Ankou-B/Pulsation-vers-DTMF/Photos/Vieille photo convertisseur nu/IMG_0514.jpg

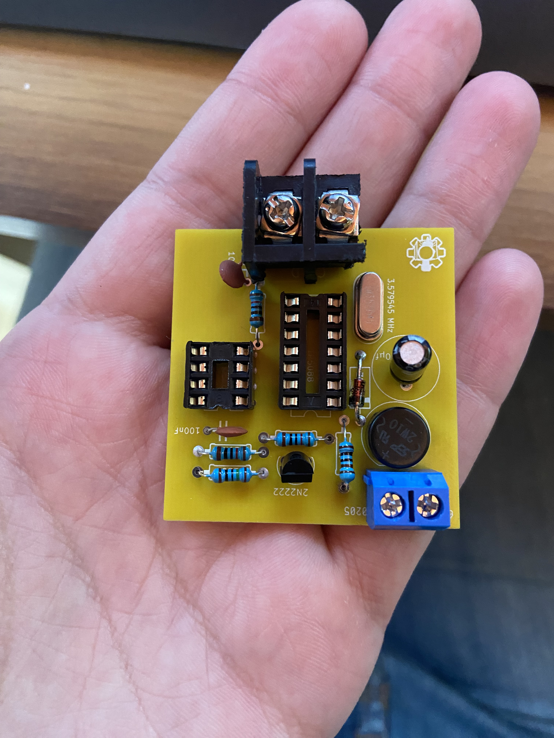
Photos/Vieille photo convertisseur nu/IMG_0514.jpg
