Ankou-B/Pulsation-vers-DTMF/Photos/Vieille photo convertisseur nu/IMG_0515.jpg

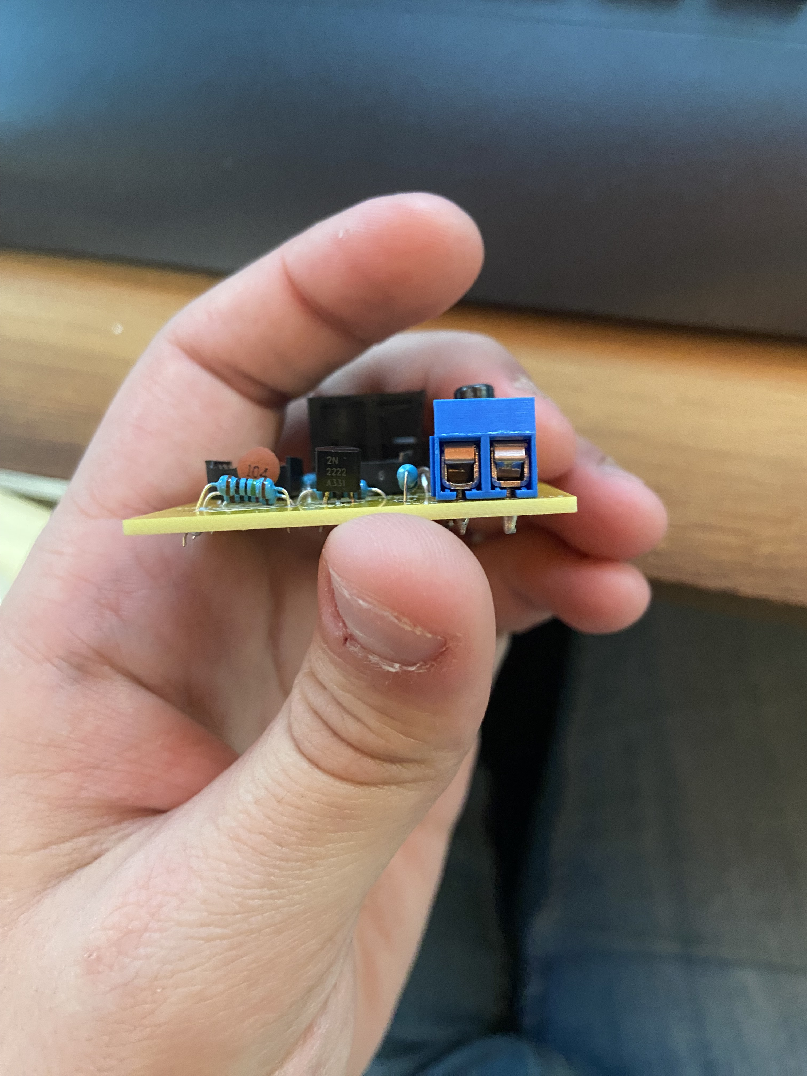
Photos/Vieille photo convertisseur nu/IMG_0515.jpg
