Ankou-B/Pulsation-vers-DTMF/Photos/Vieille photo convertisseur nu/IMG_0516.jpg

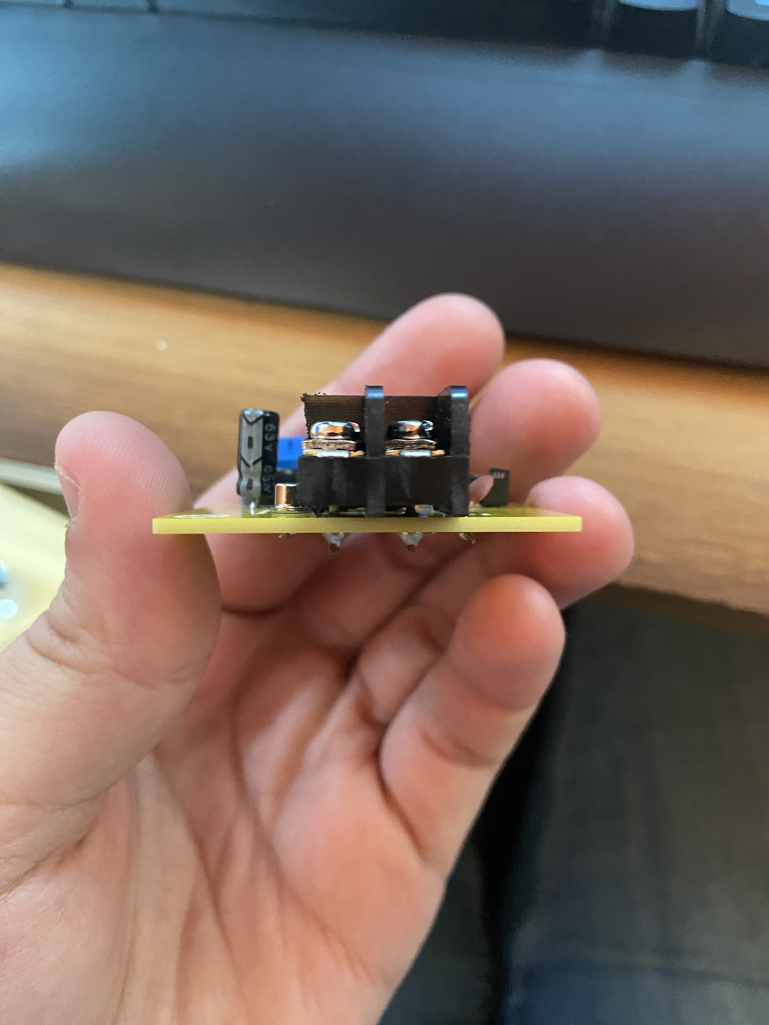
Photos/Vieille photo convertisseur nu/IMG_0516.jpg
