Ankou-B/Pulsation-vers-DTMF/Photos/Vieille photo convertisseur nu/IMG_0517.jpg

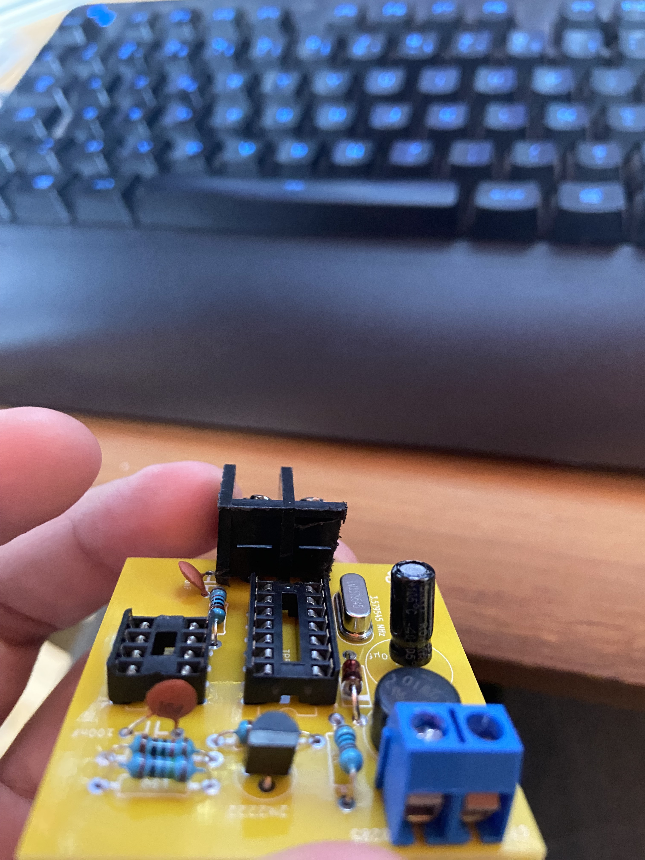
Photos/Vieille photo convertisseur nu/IMG_0517.jpg
