Ankou-B/Pulsation-vers-DTMF/Photos/Vieille photo convertisseur/1/IMG_0537.jpg

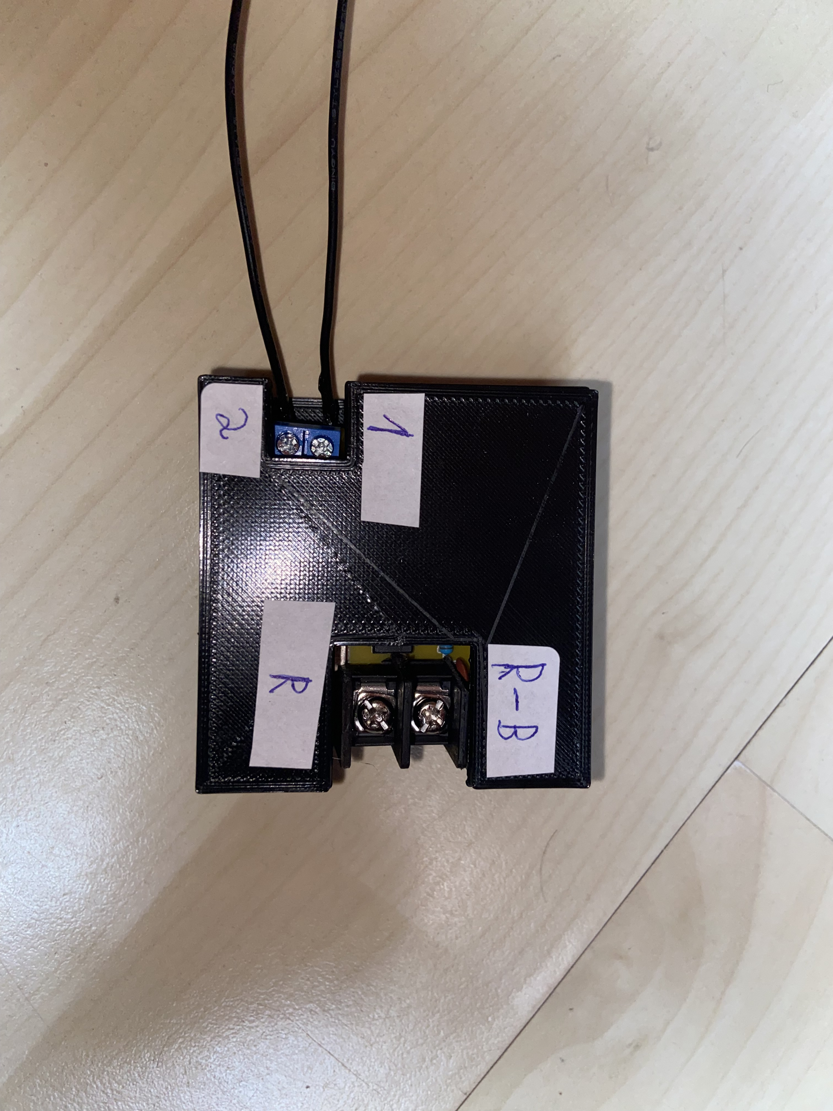
Photos/Vieille photo convertisseur/1/IMG_0537.jpg
