Ankou-B/Pulsation-vers-DTMF/Photos/Vieille photo convertisseur/2/IMG_0678.jpg

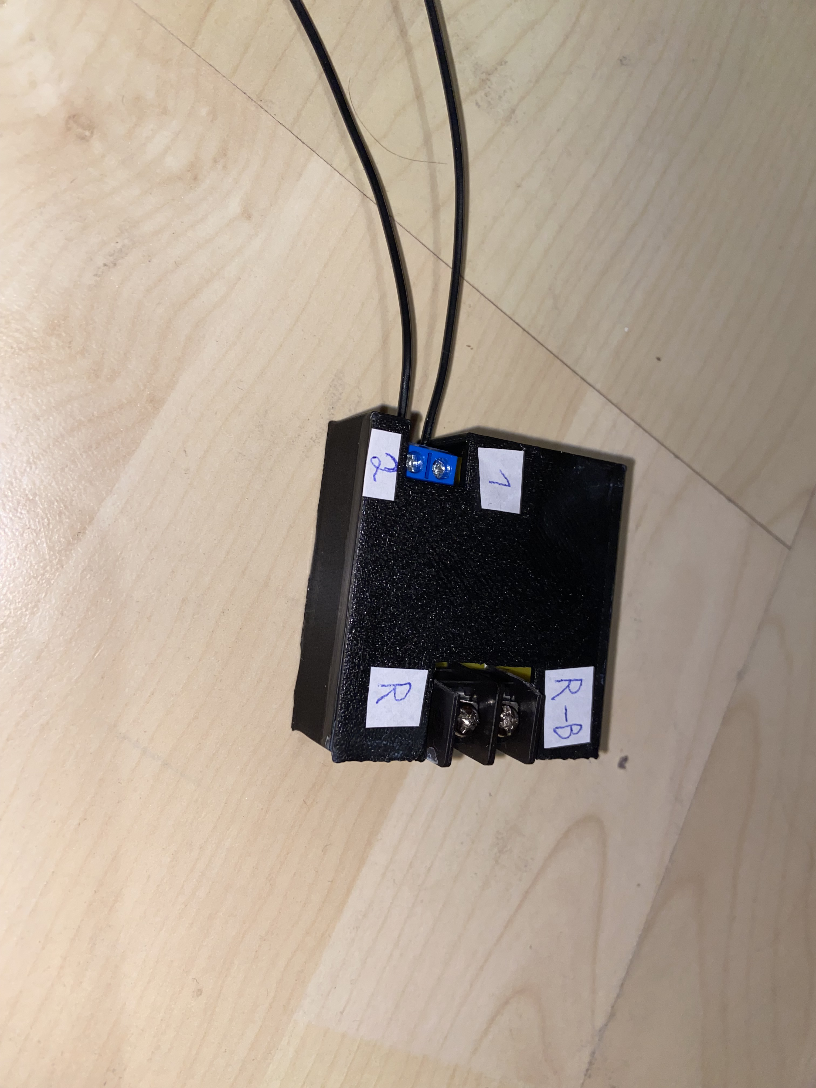
Photos/Vieille photo convertisseur/2/IMG_0678.jpg
