Ankou-B/Pulsation-vers-DTMF/Photos/Vieille photo convertisseur/3/s-l1600 (5).webp

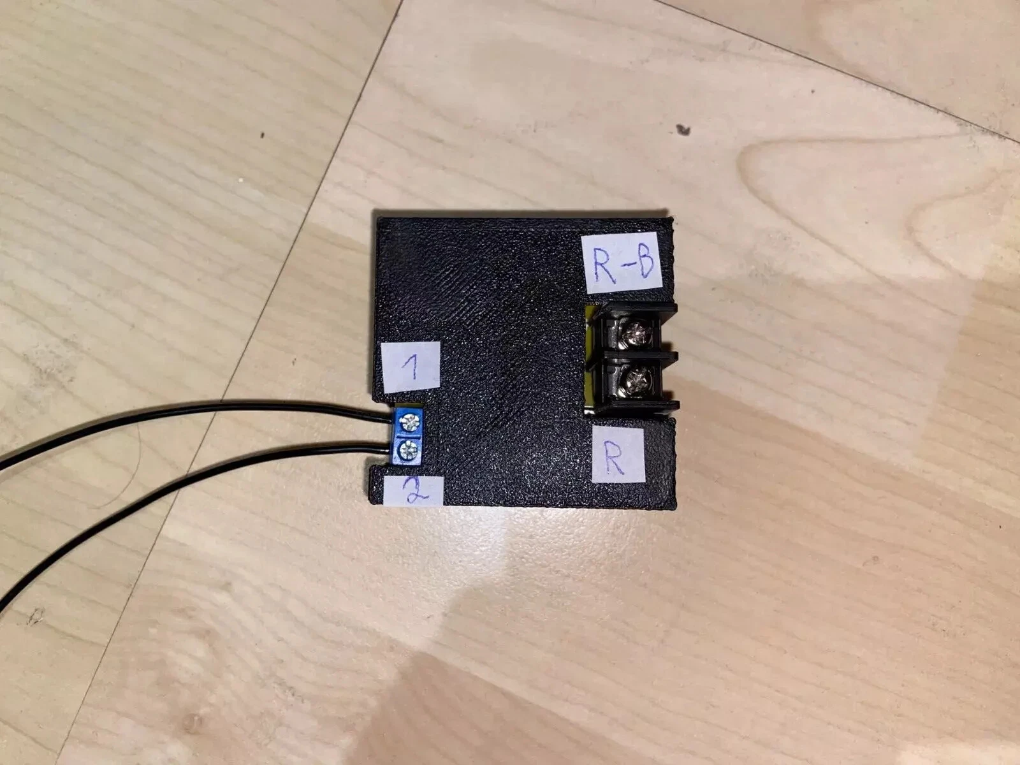
Photos/Vieille photo convertisseur/3/s-l1600 (5).webp
