Ankou-B/Pulsation-vers-DTMF/Photos/Vieille photo convertisseur/3/s-l1600 (7).webp

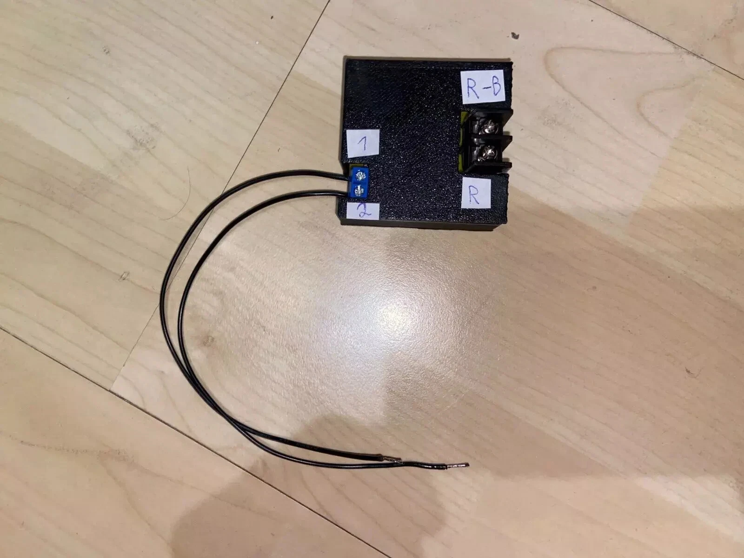
Photos/Vieille photo convertisseur/3/s-l1600 (7).webp
