Ankou-B/Pulsation-vers-DTMF/Photos/Vieille photo manuelle/IMG_0545.jpg

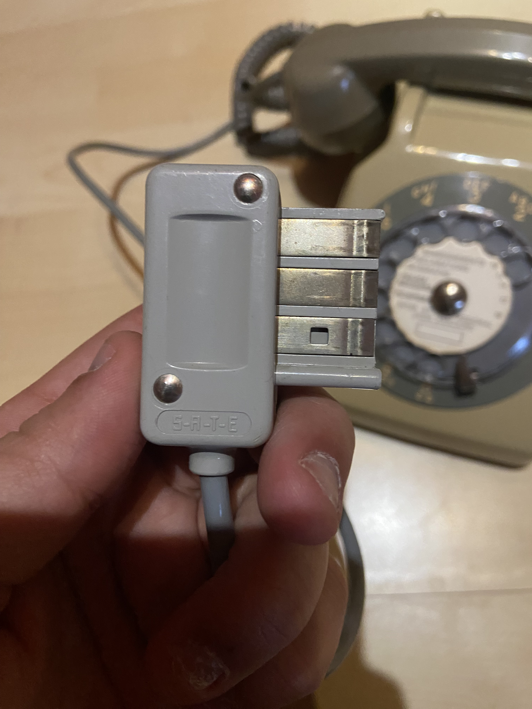
Photos/Vieille photo manuelle/IMG_0545.jpg
