Ankou-B/Pulsation-vers-DTMF/Photos/Vieille photo manuelle/IMG_0551.jpg

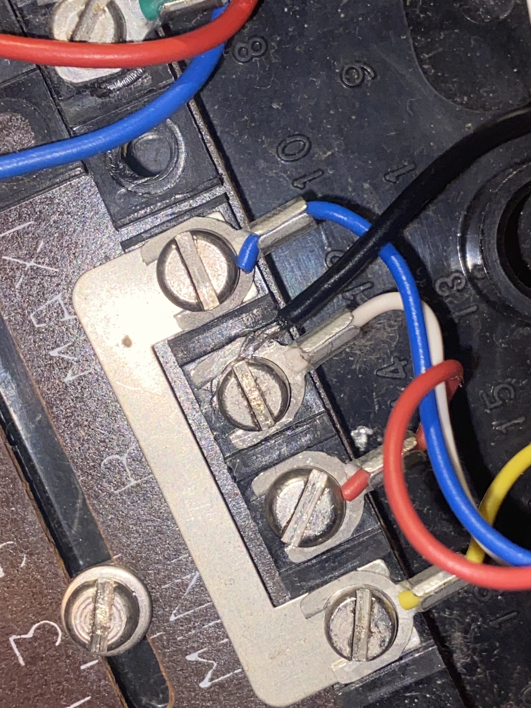
Photos/Vieille photo manuelle/IMG_0551.jpg
