Ankou-B/Pulsation-vers-DTMF/Photos/Vieille photo manuelle/IMG_0556.jpg

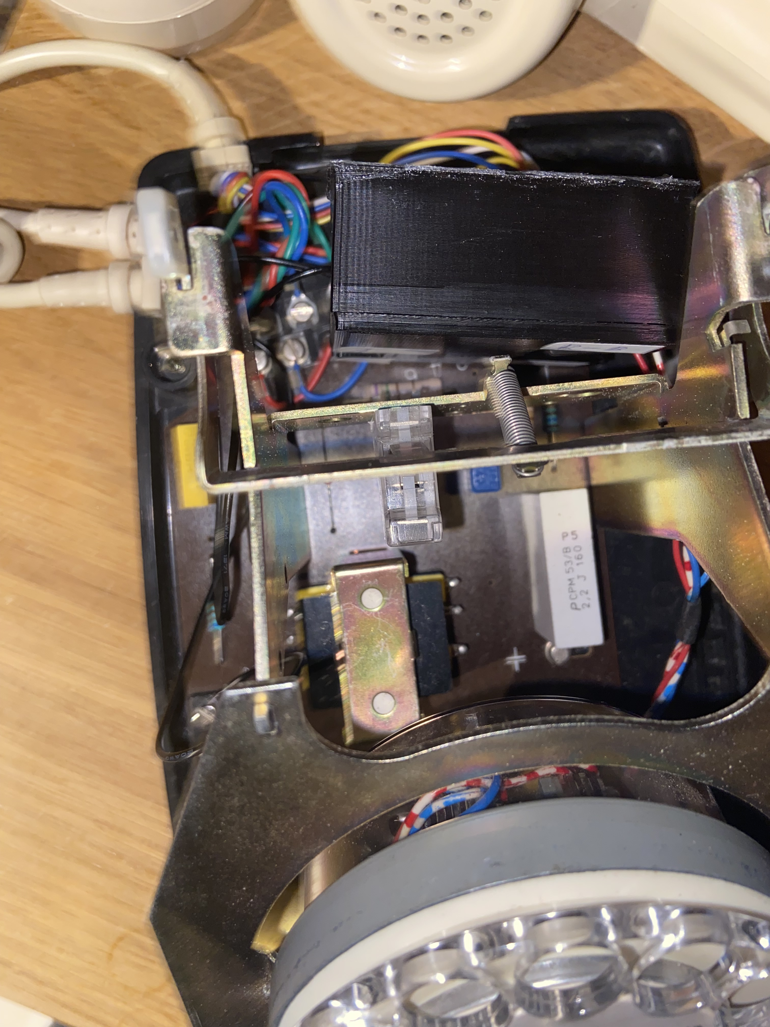
Photos/Vieille photo manuelle/IMG_0556.jpg
