Ankou-B/Pulsation-vers-DTMF/Photos/Vieille photo manuelle/IMG_0557.jpg

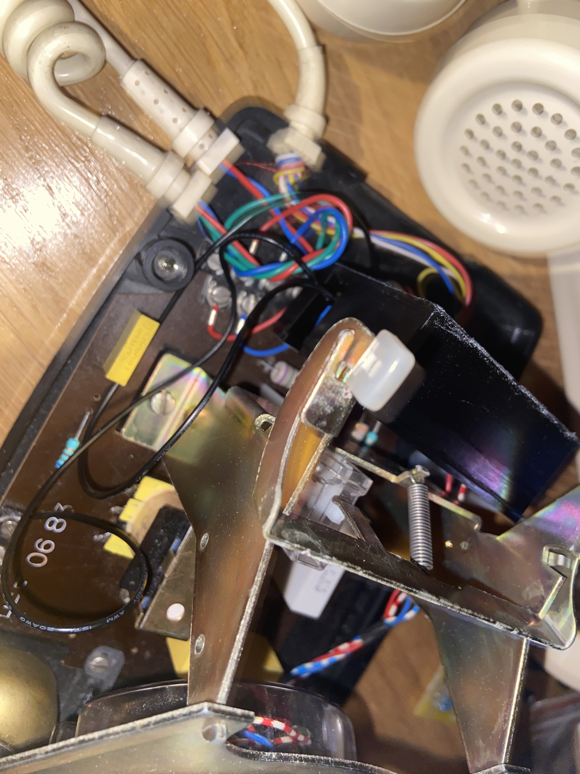
Photos/Vieille photo manuelle/IMG_0557.jpg
