Ankou-B/Pulsation-vers-DTMF/Photos/Vieille photo manuelle/IMG_0559.jpg

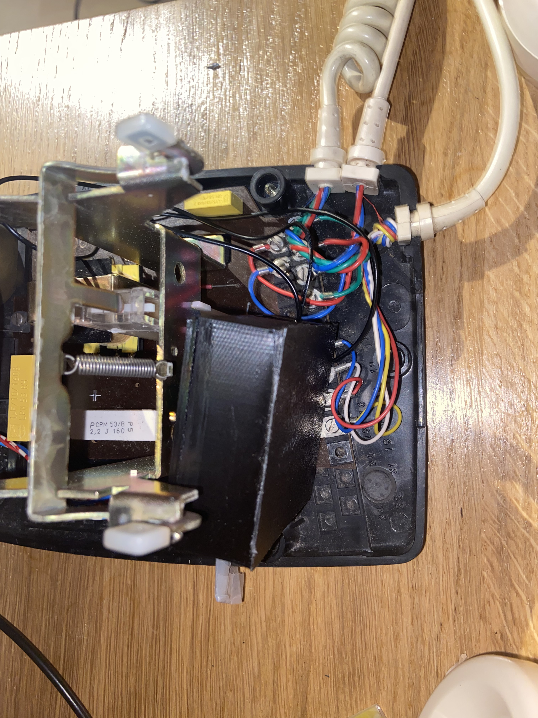
Photos/Vieille photo manuelle/IMG_0559.jpg
