Ankou-B/Pulsation-vers-DTMF/Photos/Vieille photo manuelle/IMG_0560.jpg

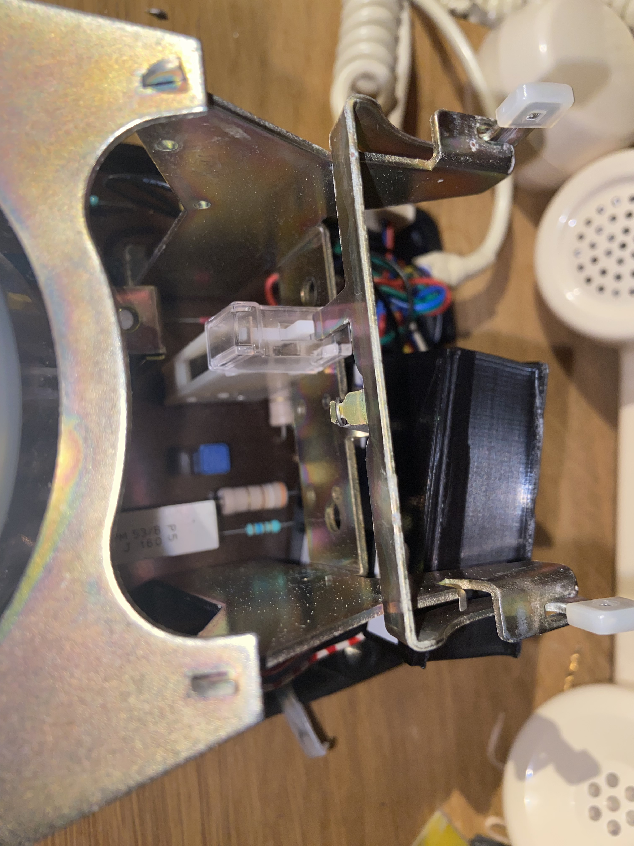
Photos/Vieille photo manuelle/IMG_0560.jpg
