Ankou-B/Pulsation-vers-DTMF/Photos/Vieille photo manuelle/IMG_0569.jpg

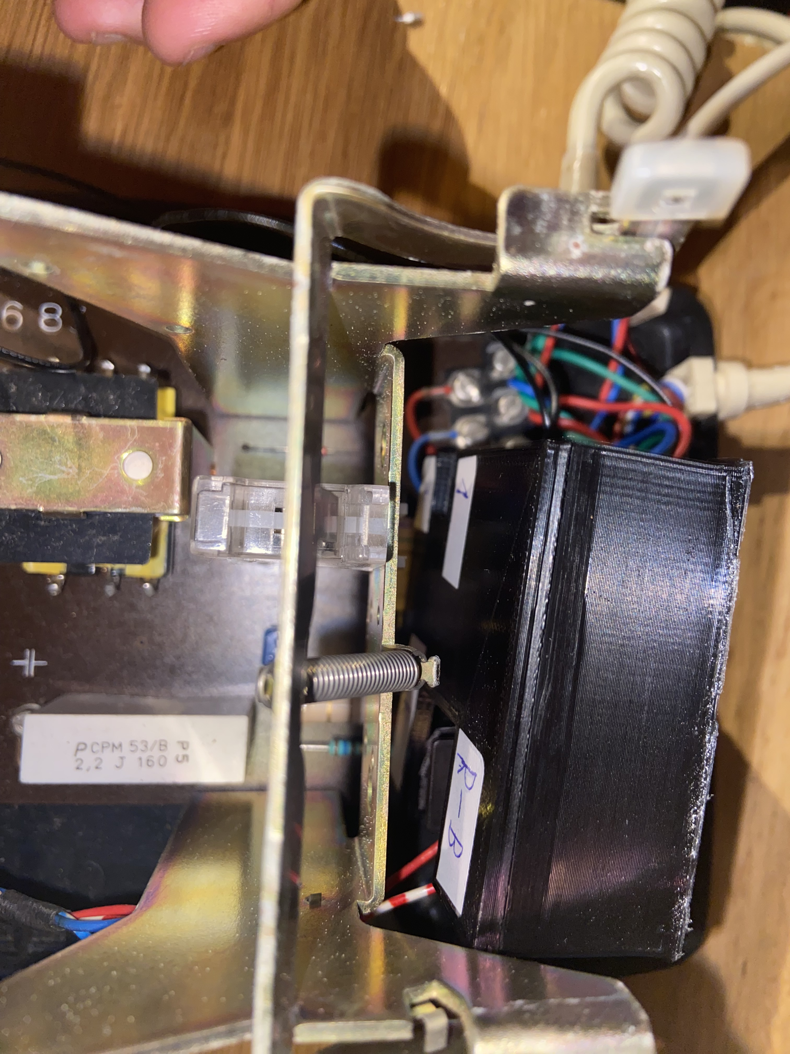
Photos/Vieille photo manuelle/IMG_0569.jpg
