Ankou-B/Pulsation-vers-DTMF/Photos/Vieille photo manuelle/IMG_0570.jpg

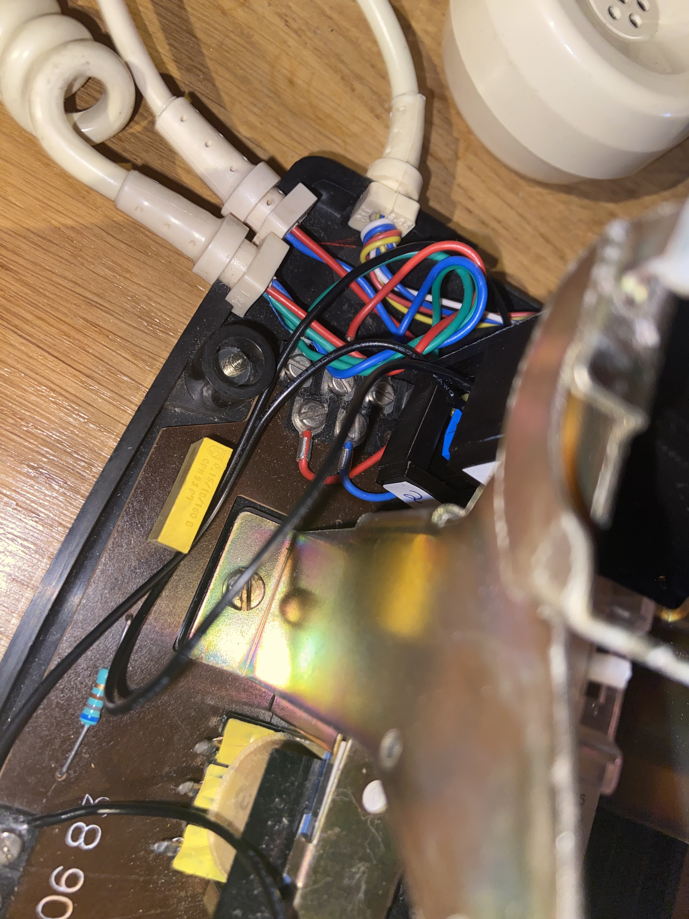
Photos/Vieille photo manuelle/IMG_0570.jpg
