Ankou-B/Pulsation-vers-DTMF/Photos/Vieille photo manuelle/IMG_0625.jpg

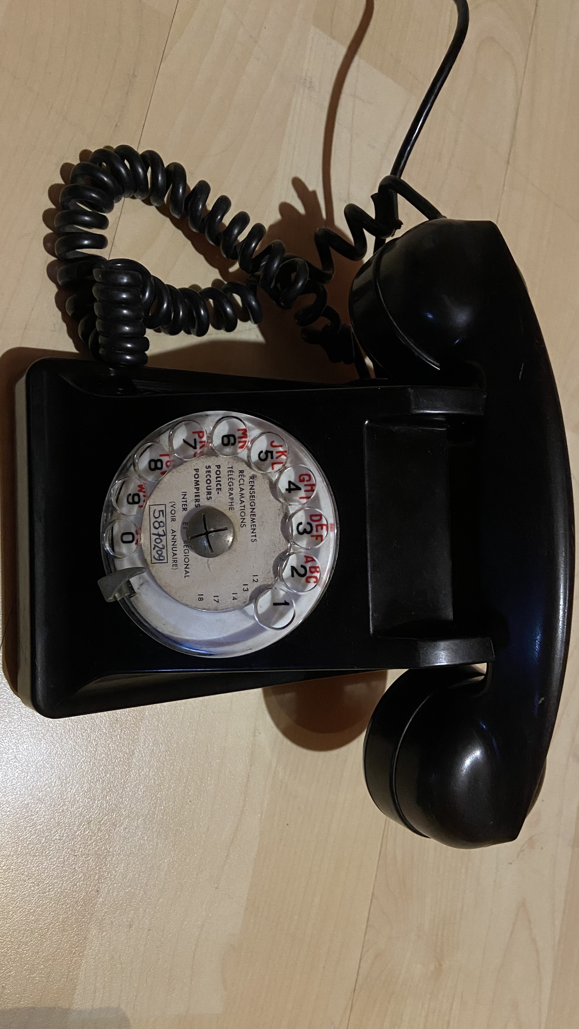
Photos/Vieille photo manuelle/IMG_0625.jpg
