Ankou-B/Pulsation-vers-DTMF/Photos/Vieille photo manuelle/IMG_0626.jpg

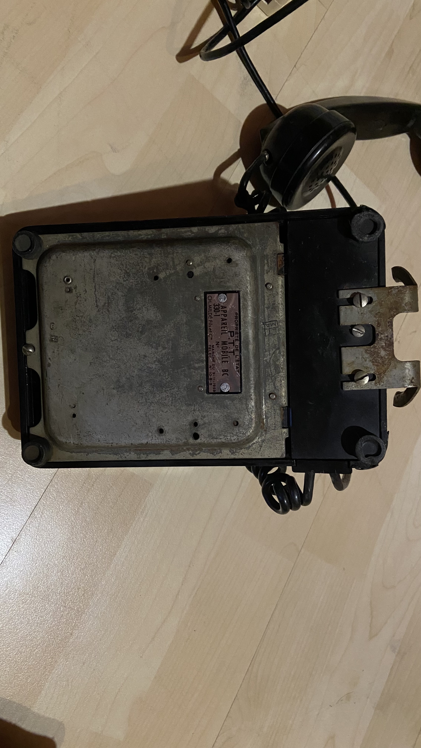
Photos/Vieille photo manuelle/IMG_0626.jpg
