Ankou-B/Pulsation-vers-DTMF/Photos/Vieille photo manuelle/IMG_0627.jpg

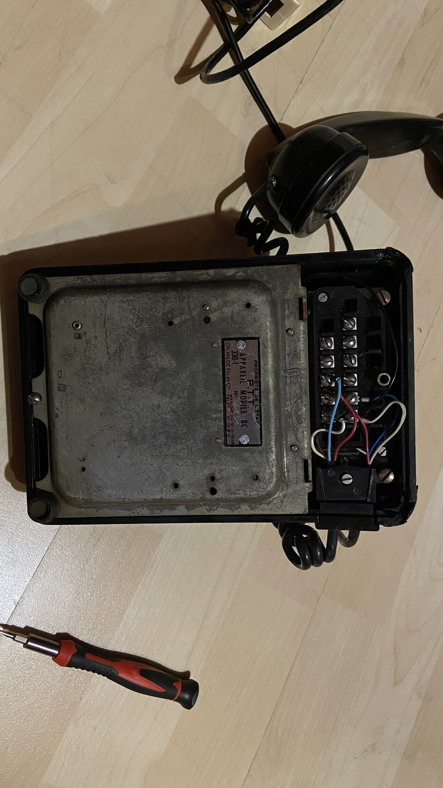
Photos/Vieille photo manuelle/IMG_0627.jpg
