Ankou-B/Pulsation-vers-DTMF/Photos/Vieille photo manuelle/IMG_0628.jpg

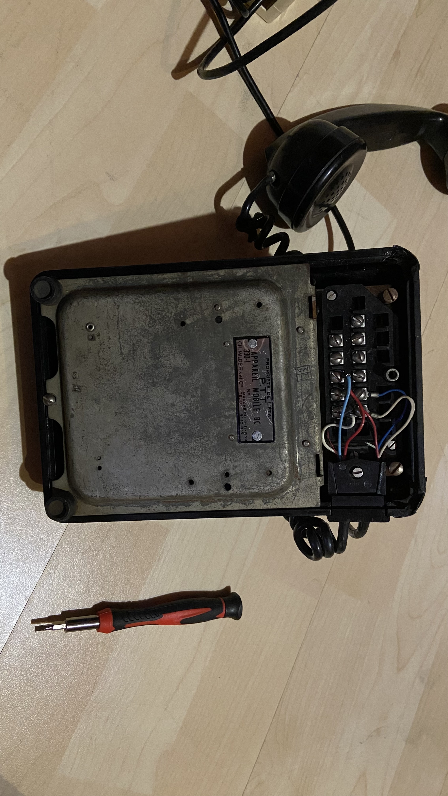
Photos/Vieille photo manuelle/IMG_0628.jpg
