Ankou-B/Pulsation-vers-DTMF/Photos/Vieille photo manuelle/IMG_0629.jpg

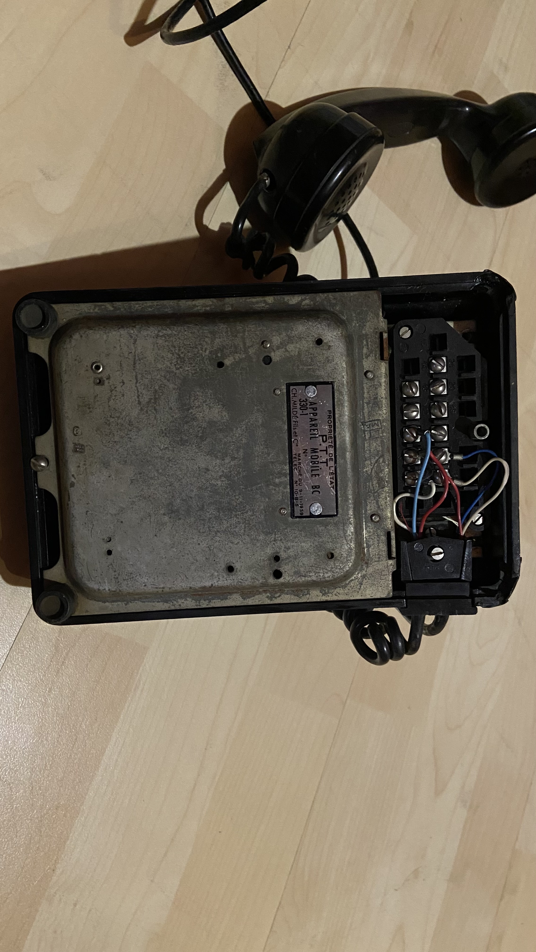
Photos/Vieille photo manuelle/IMG_0629.jpg
