Ankou-B/Pulsation-vers-DTMF/Photos/Vieille photo manuelle/IMG_0630.jpg

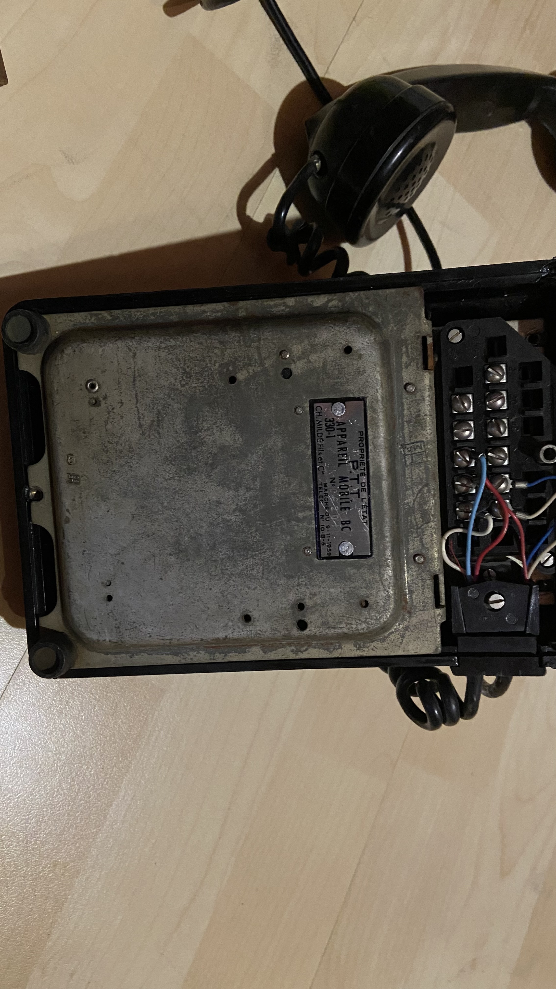
Photos/Vieille photo manuelle/IMG_0630.jpg
