Ankou-B/Pulsation-vers-DTMF/Photos/Vieille photo manuelle/IMG_0631.jpg

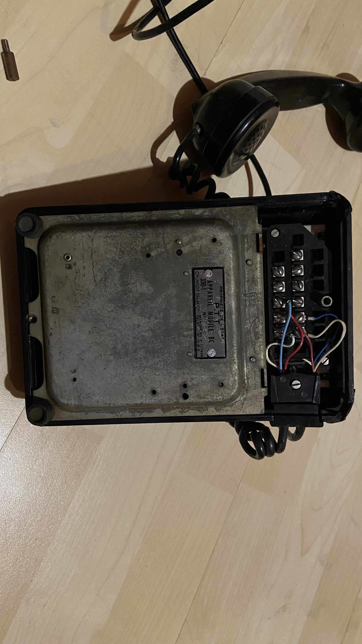
Photos/Vieille photo manuelle/IMG_0631.jpg
