Ankou-B/Pulsation-vers-DTMF/Photos/Vieille photo manuelle/IMG_0632.jpg

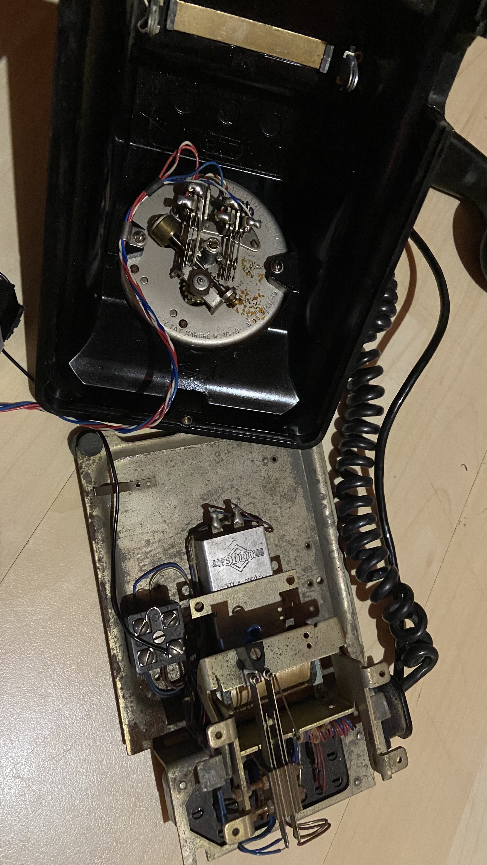
Photos/Vieille photo manuelle/IMG_0632.jpg
