Ankou-B/Pulsation-vers-DTMF/Photos/Vieille photo manuelle/IMG_0633.jpg

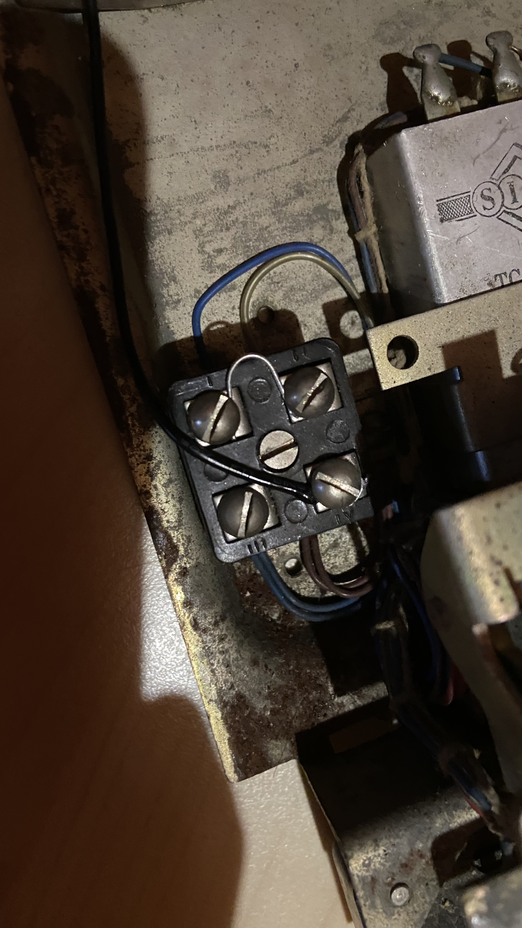
Photos/Vieille photo manuelle/IMG_0633.jpg
