Ankou-B/Pulsation-vers-DTMF/Photos/Vieille photo manuelle/IMG_0634.jpg

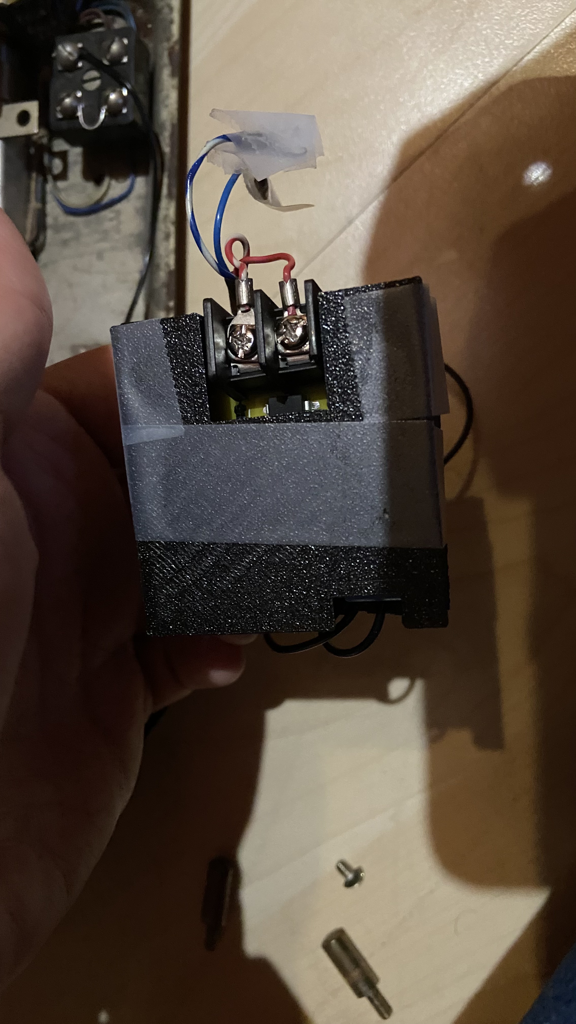
Photos/Vieille photo manuelle/IMG_0634.jpg
