Ankou-B/Pulsation-vers-DTMF/Photos/Vieille photo manuelle/IMG_0635.jpg

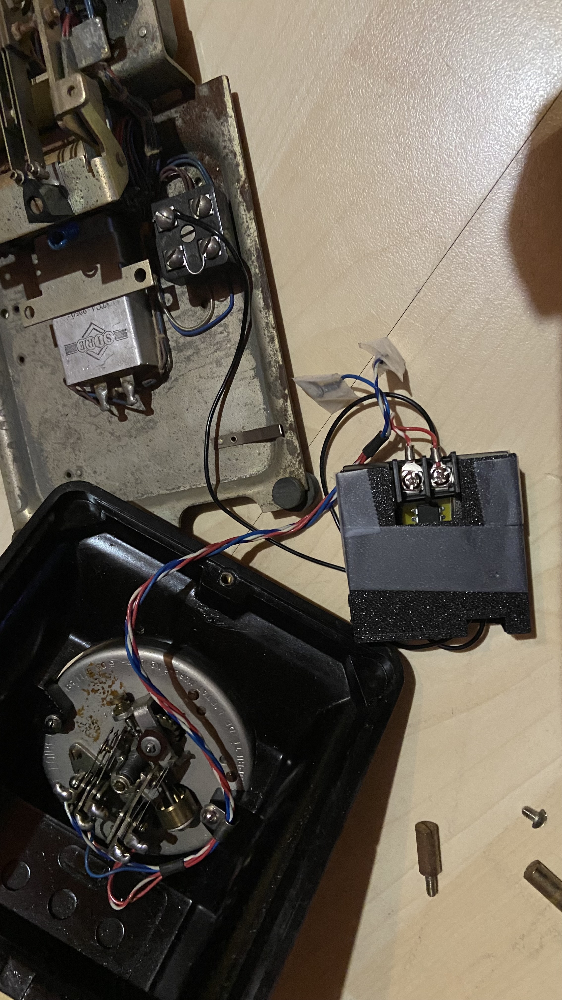
Photos/Vieille photo manuelle/IMG_0635.jpg
