Ankou-B/Pulsation-vers-DTMF/Photos/Vieille photo manuelle/IMG_0636.jpg

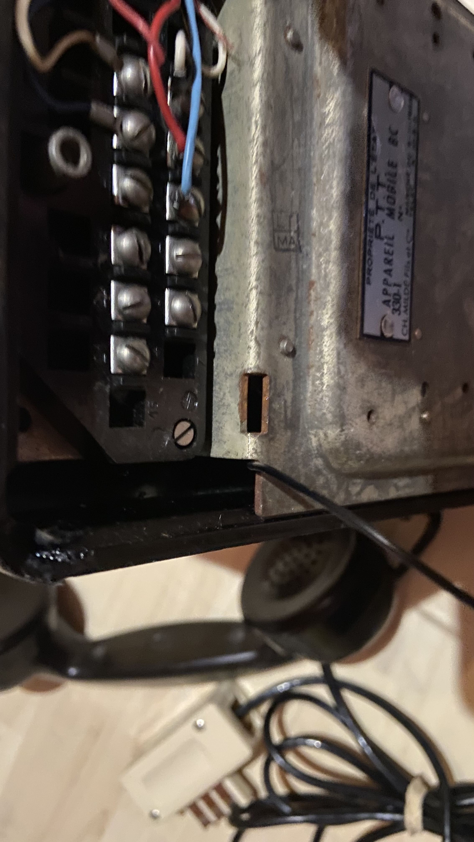
Photos/Vieille photo manuelle/IMG_0636.jpg
