Ankou-B/Pulsation-vers-DTMF/Photos/Vieille photo manuelle/IMG_0637.jpg

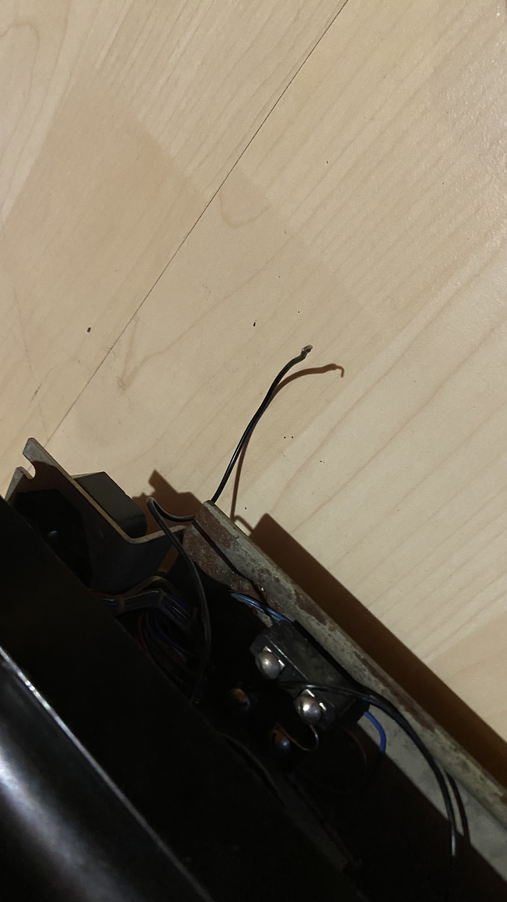
Photos/Vieille photo manuelle/IMG_0637.jpg
