Ankou-B/Pulsation-vers-DTMF/Photos/Vieille photo manuelle/IMG_0638.jpg

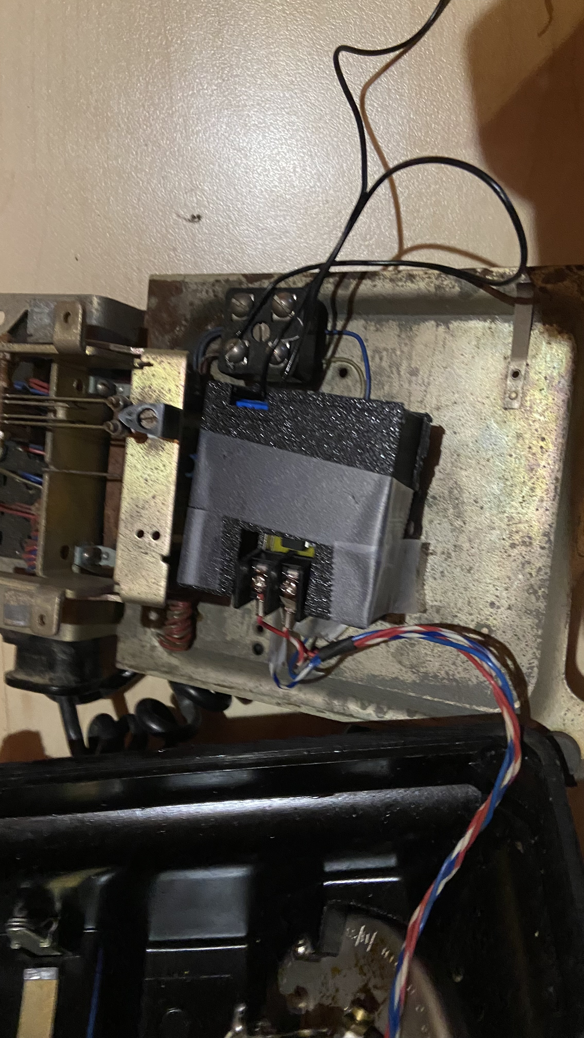
Photos/Vieille photo manuelle/IMG_0638.jpg
