Ankou-B/Pulsation-vers-DTMF/Photos/Vieille photo manuelle/IMG_0639.jpg

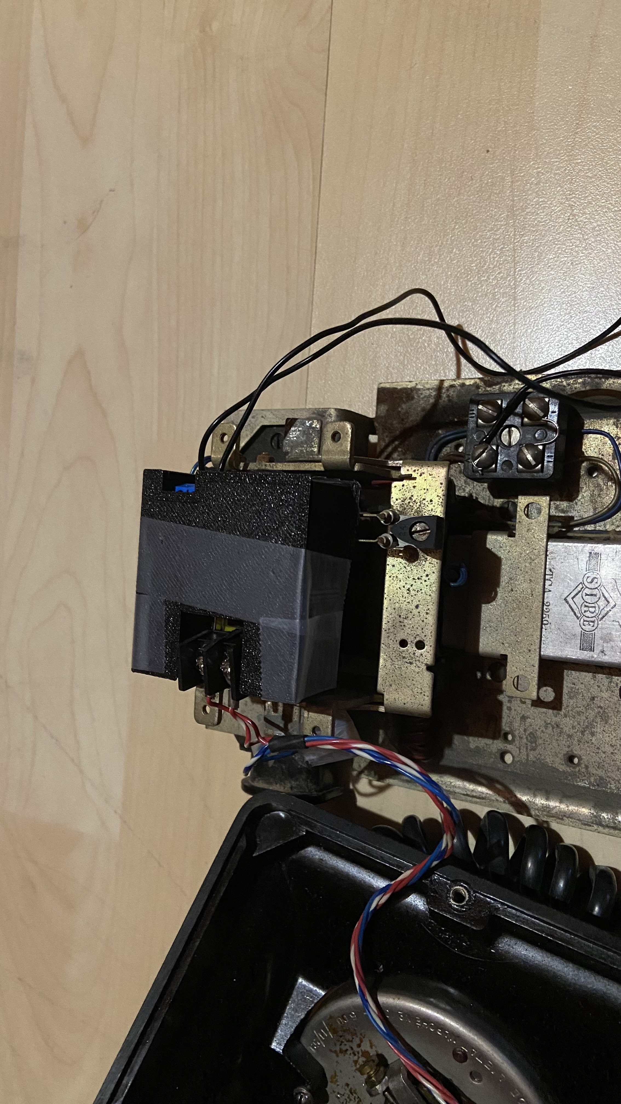
Photos/Vieille photo manuelle/IMG_0639.jpg
