Ankou-B/Pulsation-vers-DTMF/Photos/Vieille photo manuelle/IMG_0640.jpg

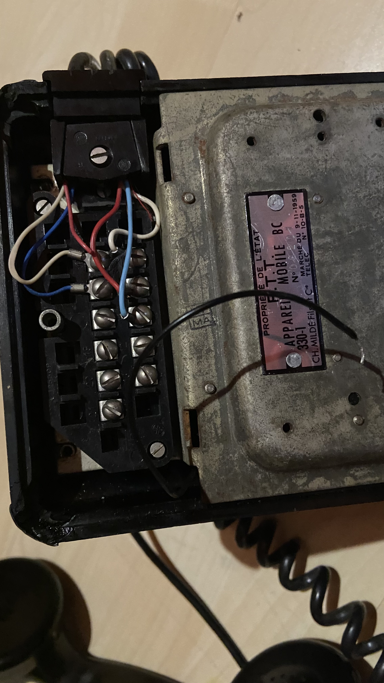
Photos/Vieille photo manuelle/IMG_0640.jpg
