Ankou-B/Pulsation-vers-DTMF/Photos/Vieille photo manuelle/IMG_0641.jpg

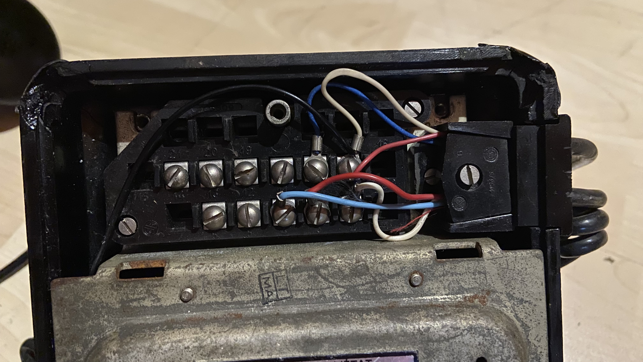
Photos/Vieille photo manuelle/IMG_0641.jpg
