Ankou-B/Pulsation-vers-DTMF/Photos/Vieille photo convertisseur/1/IMG_0575.jpg

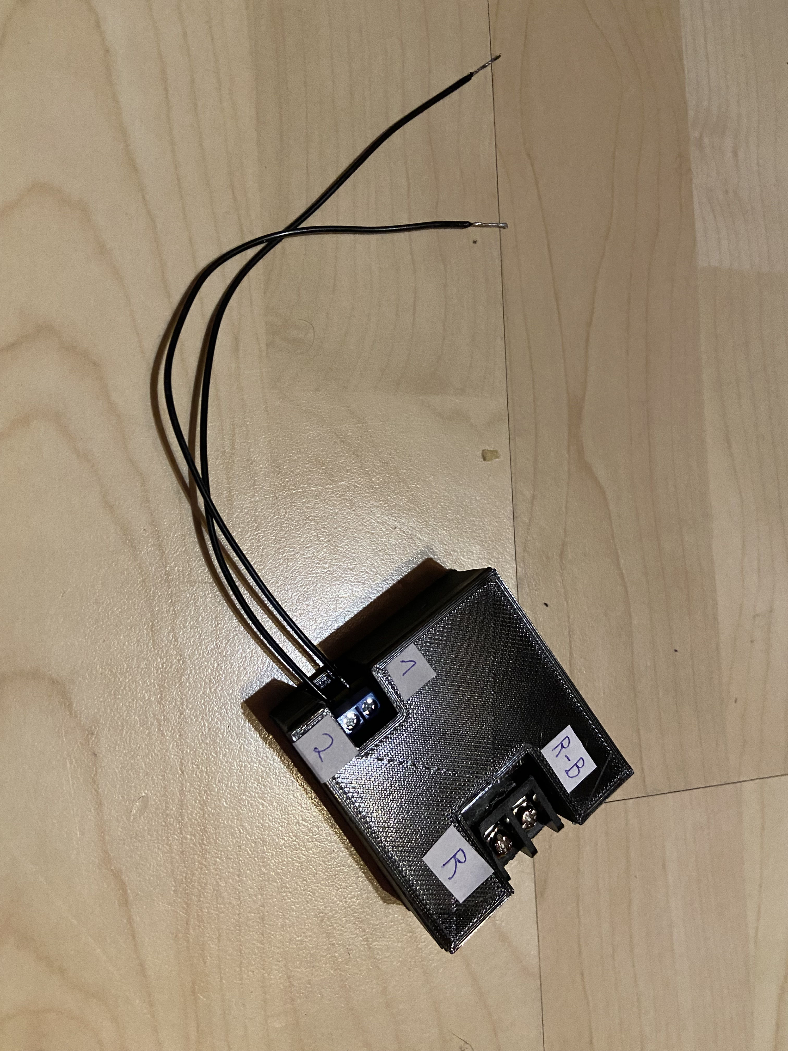
Photos/Vieille photo convertisseur/1/IMG_0575.jpg
