Ankou-B/Pulsation-vers-DTMF/Photos/Vieille photo manuelle/IMG_0548.jpg

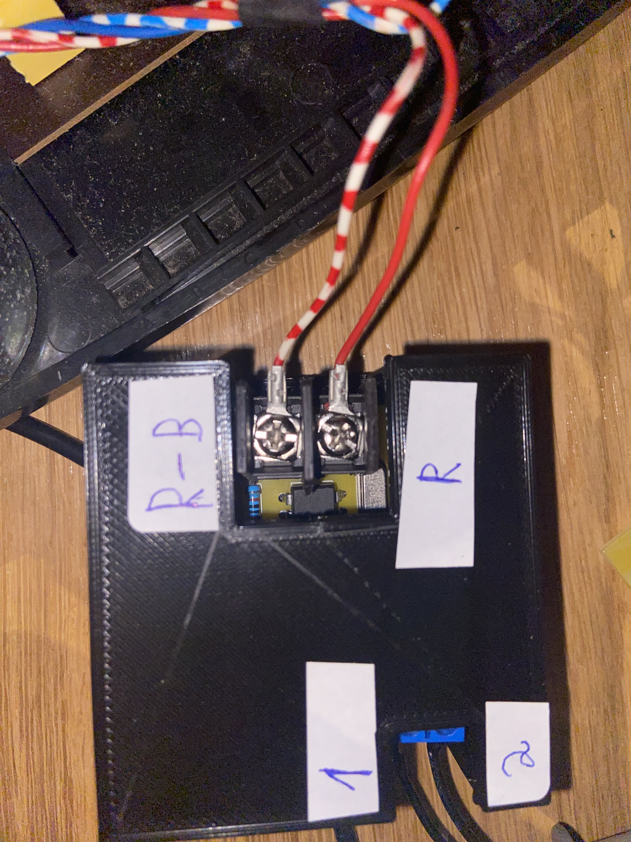
Photos/Vieille photo manuelle/IMG_0548.jpg
