Ankou-B/Pulsation-vers-DTMF/Photos/Vieille photo manuelle/IMG_0549.jpg

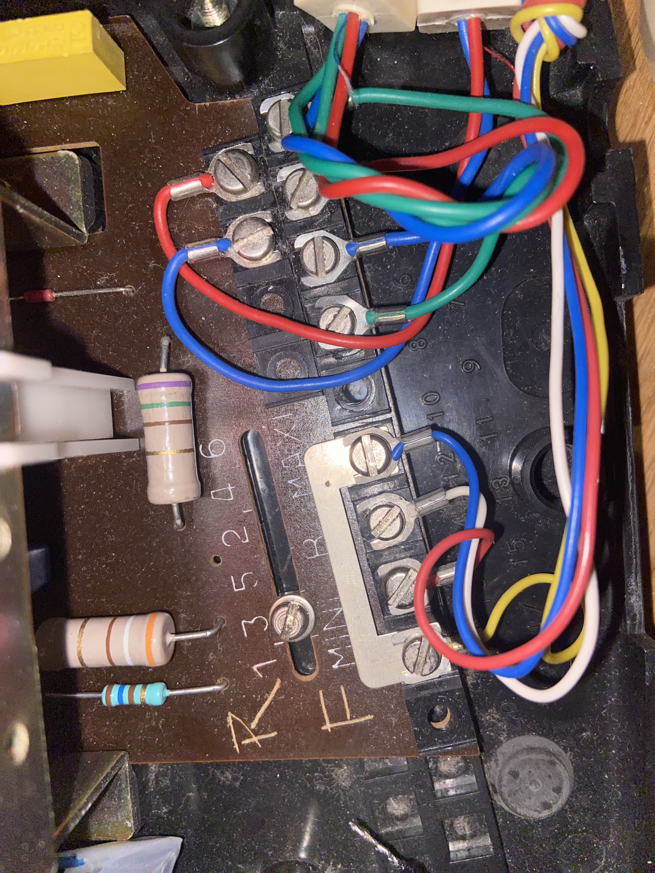
Photos/Vieille photo manuelle/IMG_0549.jpg
