Ankou-B/Pulsation-vers-DTMF/Photos/Vieille photo manuelle/IMG_0550.jpg

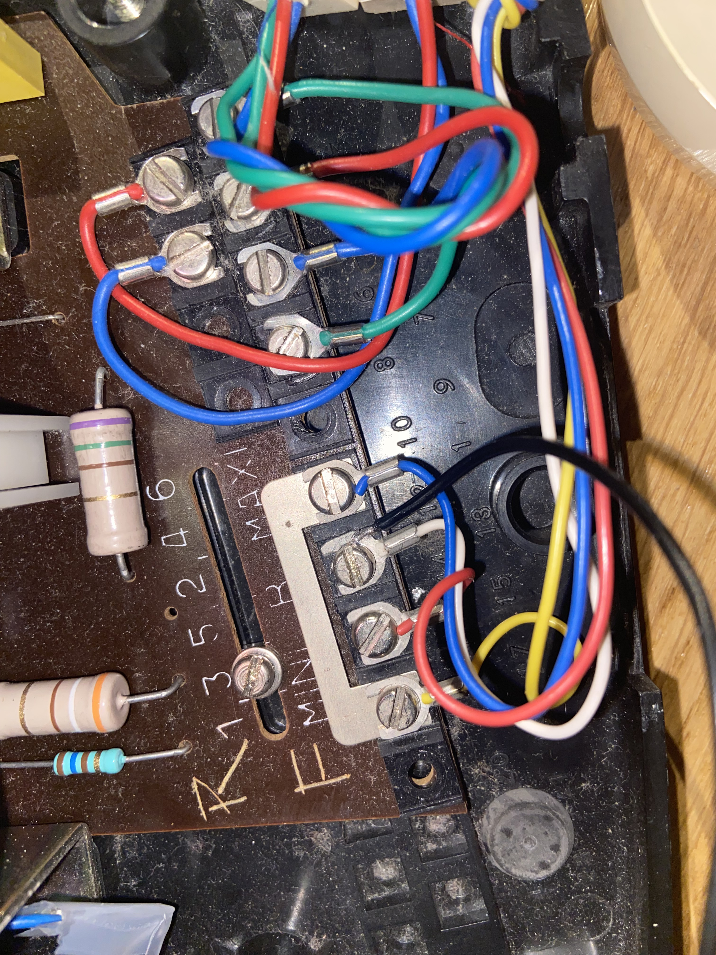
Photos/Vieille photo manuelle/IMG_0550.jpg
