Ankou-B/Pulsation-vers-DTMF/Photos/Vieille photo manuelle/IMG_0552.jpg

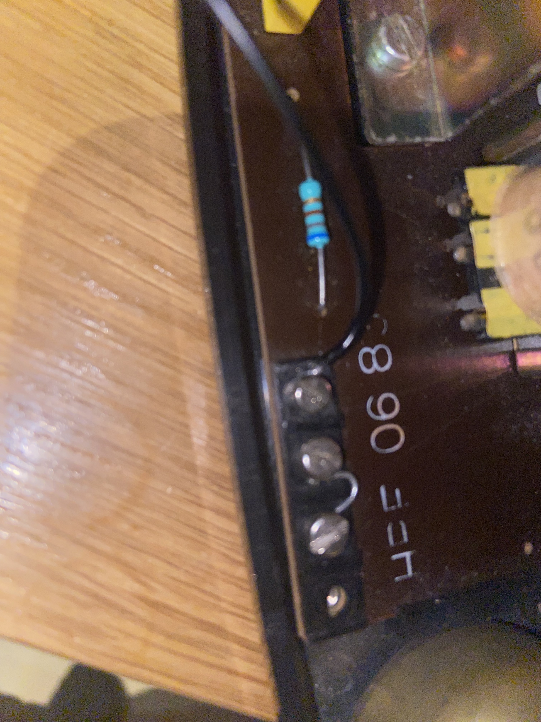
Photos/Vieille photo manuelle/IMG_0552.jpg
