Ankou-B/Pulsation-vers-DTMF/Photos/Vieille photo manuelle/IMG_0553.jpg

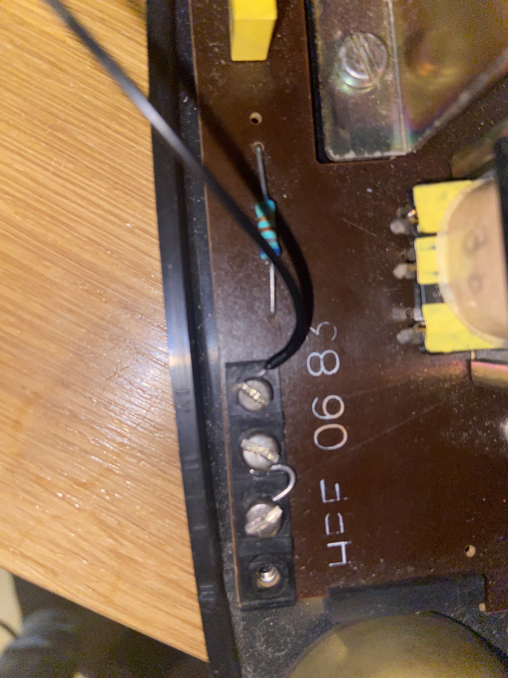
Photos/Vieille photo manuelle/IMG_0553.jpg
