Ankou-B/Pulsation-vers-DTMF/Photos/Vieille photo manuelle/IMG_0555.jpg

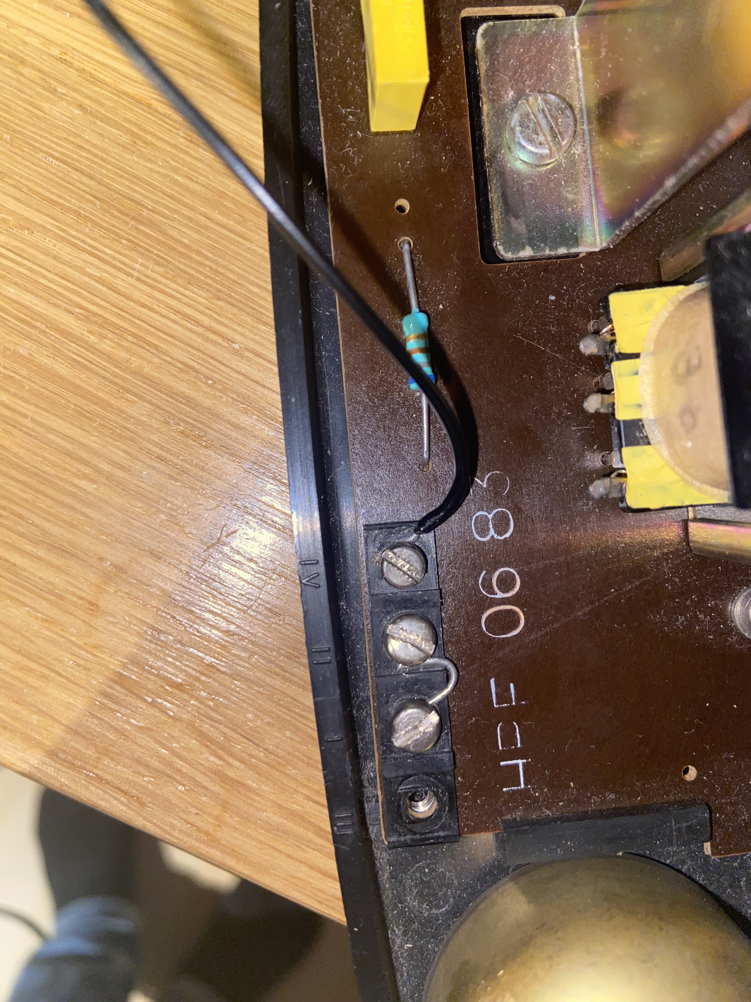
Photos/Vieille photo manuelle/IMG_0555.jpg
