Ankou-B/Pulsation-vers-DTMF/Photos/Vieille photo manuelle/IMG_0567.jpg

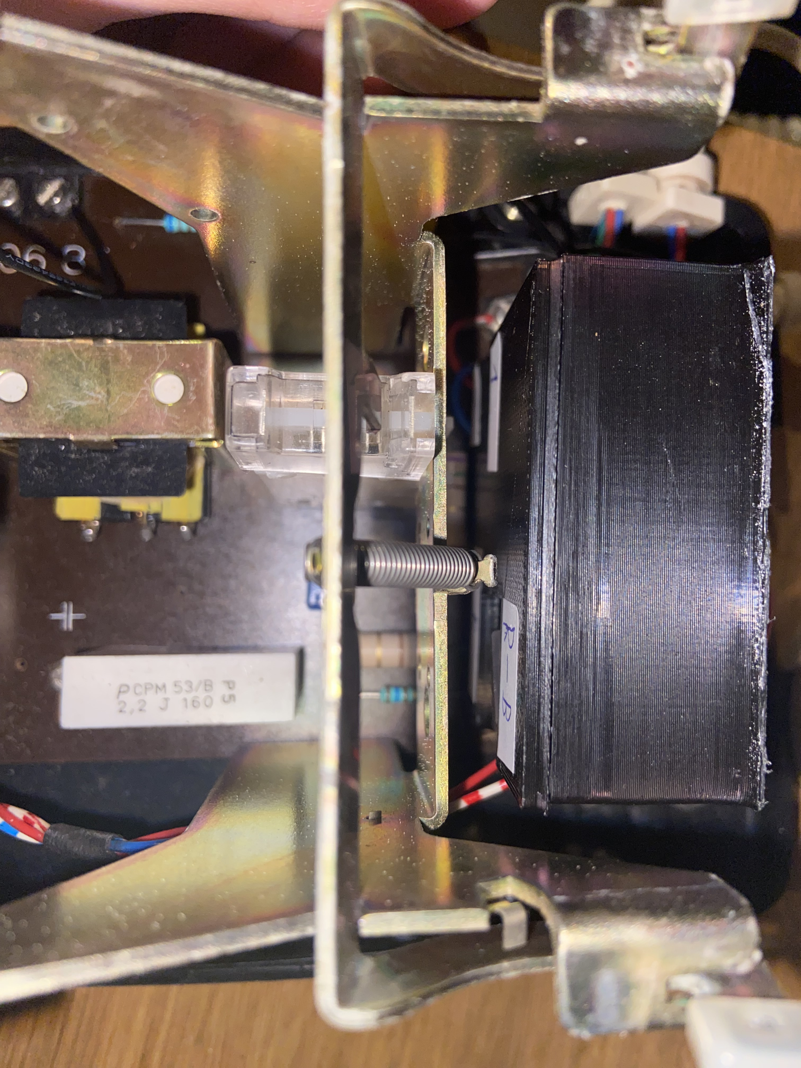
Photos/Vieille photo manuelle/IMG_0567.jpg
