Ankou-B/Pulsation-vers-DTMF/Photos/Vieille photo manuelle/IMG_0568.jpg

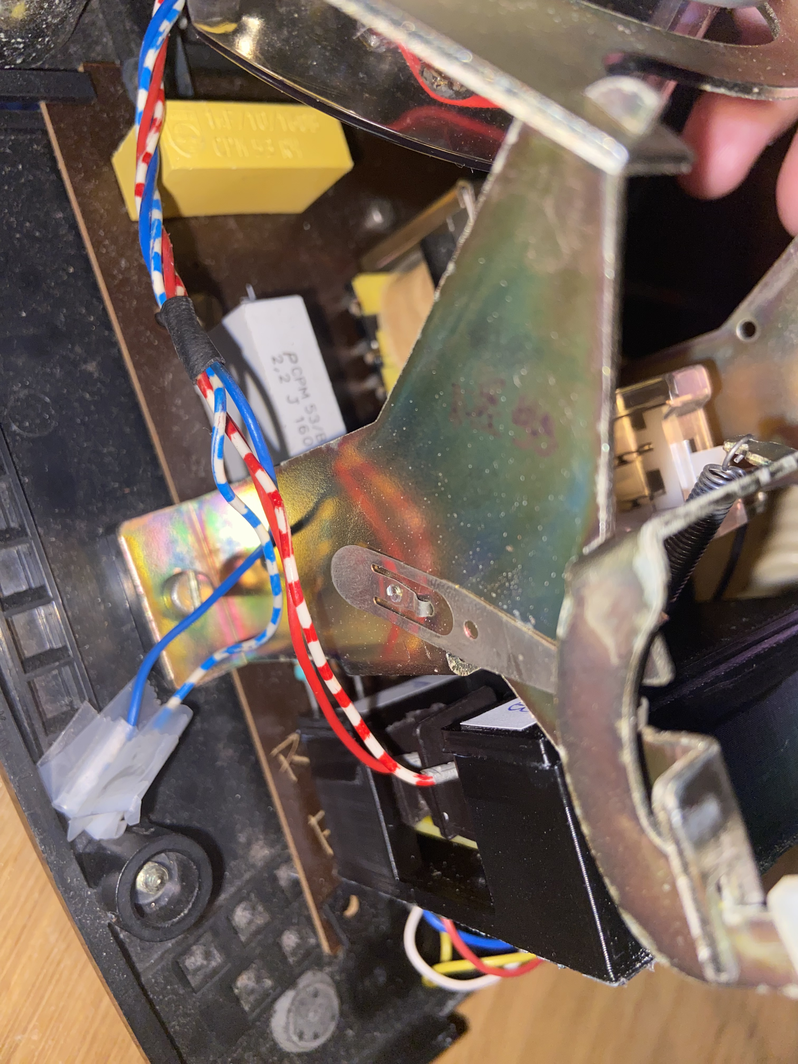
Photos/Vieille photo manuelle/IMG_0568.jpg
